atoomnetmarc/IoT12/firmware/Main processor/src/config.cpp

/*

Copyright 2021-2025 Marc Ketel
SPDX-License-Identifier: Apache-2.0

*/

const char *ssid = WIFI_SSID;
const char *password = WIFI_PASSWORD;

const char *otapassword = OTA_PASSWORD;
const char *otahostname = HOSTNAME;
