atoomnetmarc/IoT12/firmware/Main processor/include/webserverc.h

/*

Copyright 2021-2025 Marc Ketel
SPDX-License-Identifier: Apache-2.0

*/

#ifndef webserver_h
#define webserver_h

#include <WebServer.h>

extern WebServer HTTPServer;

void WebservercSetup(void);
void WebservercLoop(void);
void WebservercOnWiFiConnect(void);

#endif
